aotta/PiRTOIIDuo/PiRTOIIDuo/dir_entry.hpp

////////////////////////////////////////////////////////////////////////////////////
typedef struct {
	char isDir;
	char filename[40];
	char long_filename[64];
	char full_path[99];
} DIR_ENTRY;	// 256 bytes = 256 entries in 64k

int num_dir_entries = 0; // how many entries in the current directory

int entry_compare(const void* p1, const void* p2)
{
	DIR_ENTRY* e1 = (DIR_ENTRY*)p1;
	DIR_ENTRY* e2 = (DIR_ENTRY*)p2;
	if (e1->isDir && !e2->isDir) return -1;
	else if (!e1->isDir && e2->isDir) return 1;
	else return strcasecmp(e1->long_filename, e2->long_filename);
}

char *get_filename_ext(char *filename) {
    char *dot = strrchr(filename, '.');
    if(!dot || dot == filename) return const_cast<char*>("");
    return dot + 1;
}

int is_valid_file(char *filename) {
	char *ext = get_filename_ext(filename);
	if (strcasecmp(ext, "BIN") == 0 ) 
		return 1;
	return 0;
}
